kpierzynski/MiniEmpathiaBot/kicad_workspace/3d_models/magnetic-encoder-pair-kit-for-micro-metal-gearmotors-hpcb-compatible-w1r02a.step

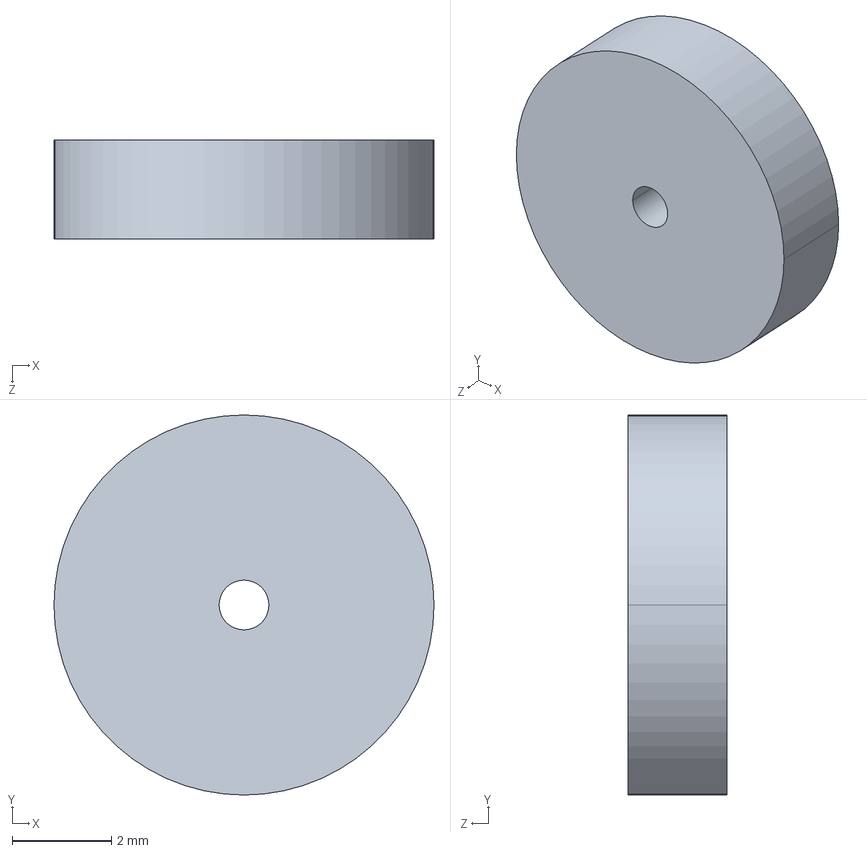
[picture p30: CAD file, 2023-08-09]
kicad_workspace/3d_models/magnetic-encoder-pair-kit-for-micro-metal-gearmotors-hpcb-compatible-w1r02a.step
7.65 x 7.65 x 2.00 mm
