kpierzynski/MiniEmpathiaBot/kicad_workspace/3d_models/magnetic-encoder-pair-kit-for-micro-metal-gearmotors-hpcb-compatible-enc03b.step

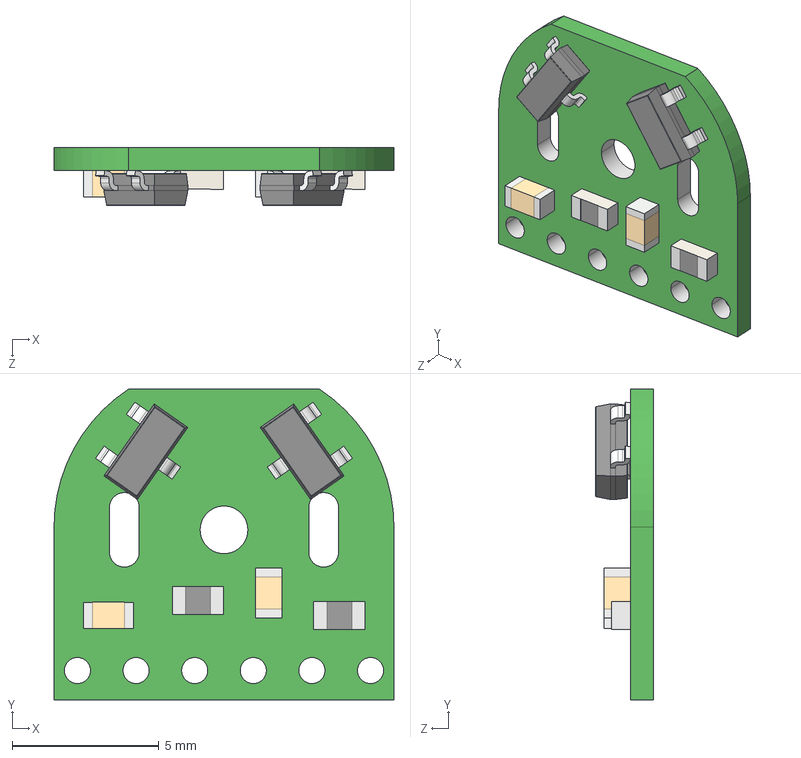
[picture p31: CAD file, 2023-08-09]
kicad_workspace/3d_models/magnetic-encoder-pair-kit-for-micro-metal-gearmotors-hpcb-compatible-enc03b.step
11.6 x 10.6 x 1.99 mm
